EmaNeg/Power_Management_Unit_Tesi/Docs/Images/BAT_sym.png

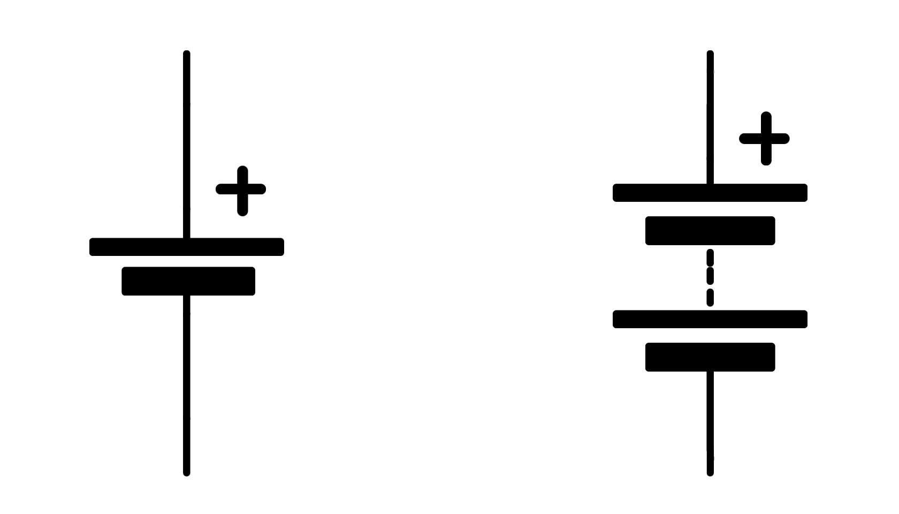
Docs/Images/BAT_sym.png
