EmaNeg/Power_Management_Unit_Tesi/Docs/Images/boost_schema.png

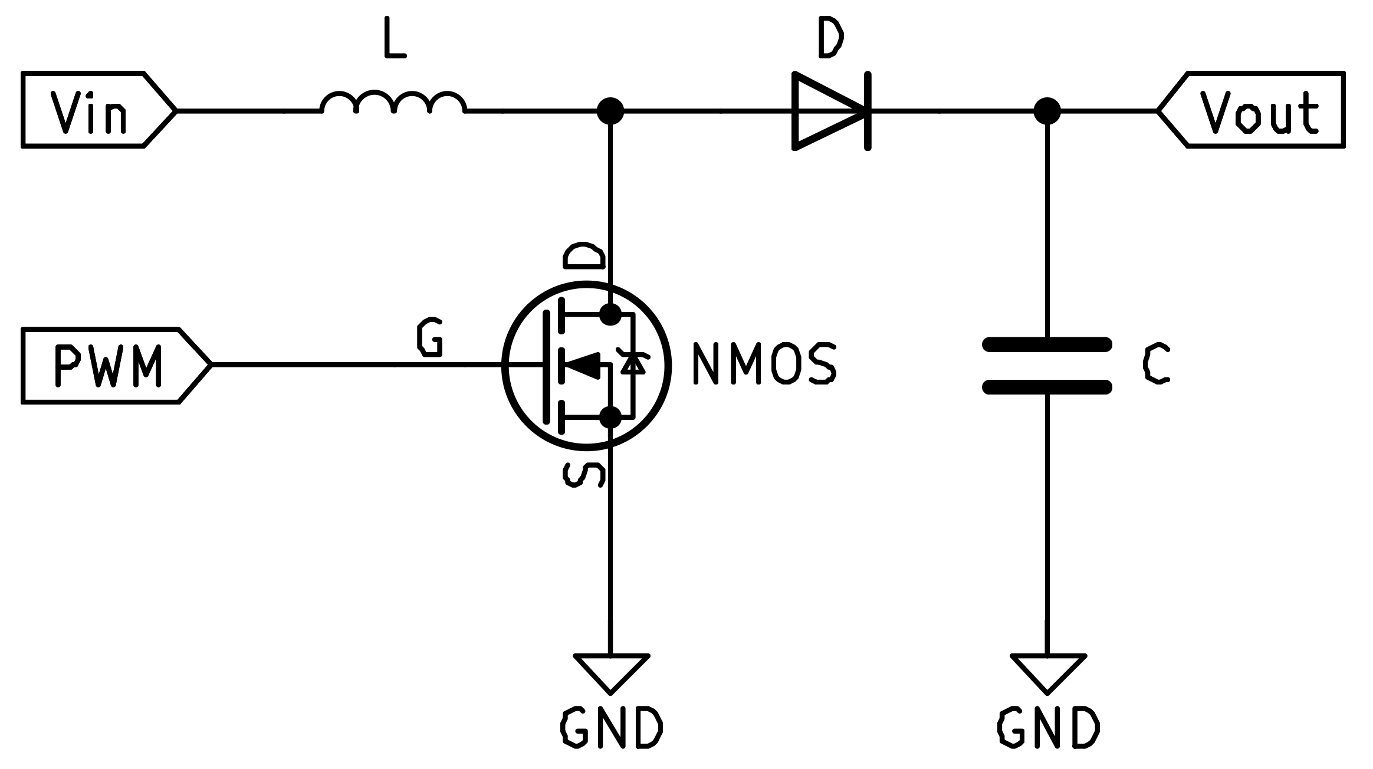
Docs/Images/boost_schema.png
