EmaNeg/Power_Management_Unit_Tesi/Docs/Images/bottom_real.png

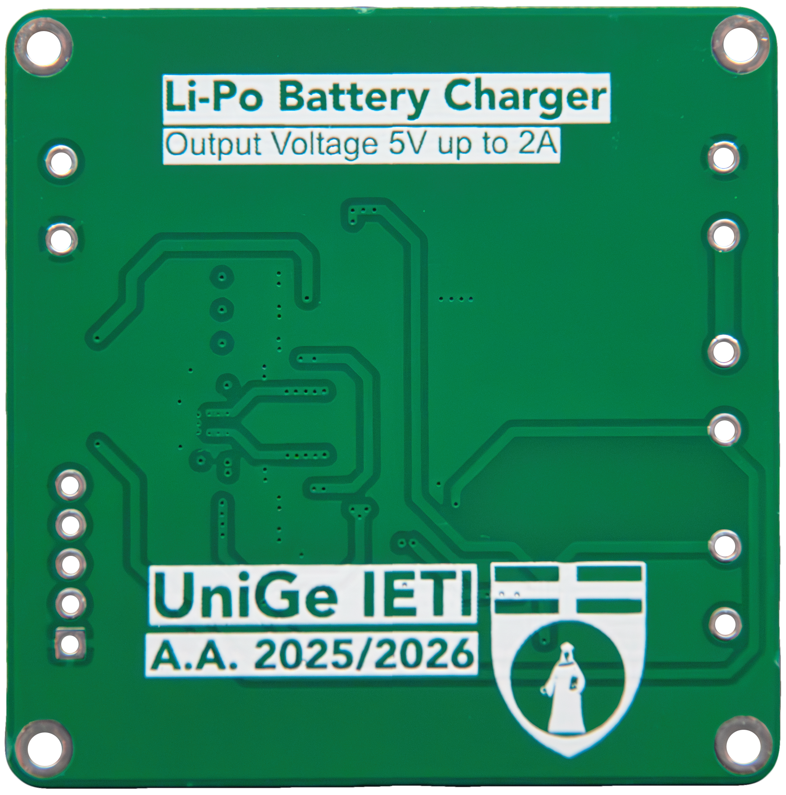
Docs/Images/bottom_real.png
