EmaNeg/Power_Management_Unit_Tesi/Docs/Images/buck-boost_schema.png

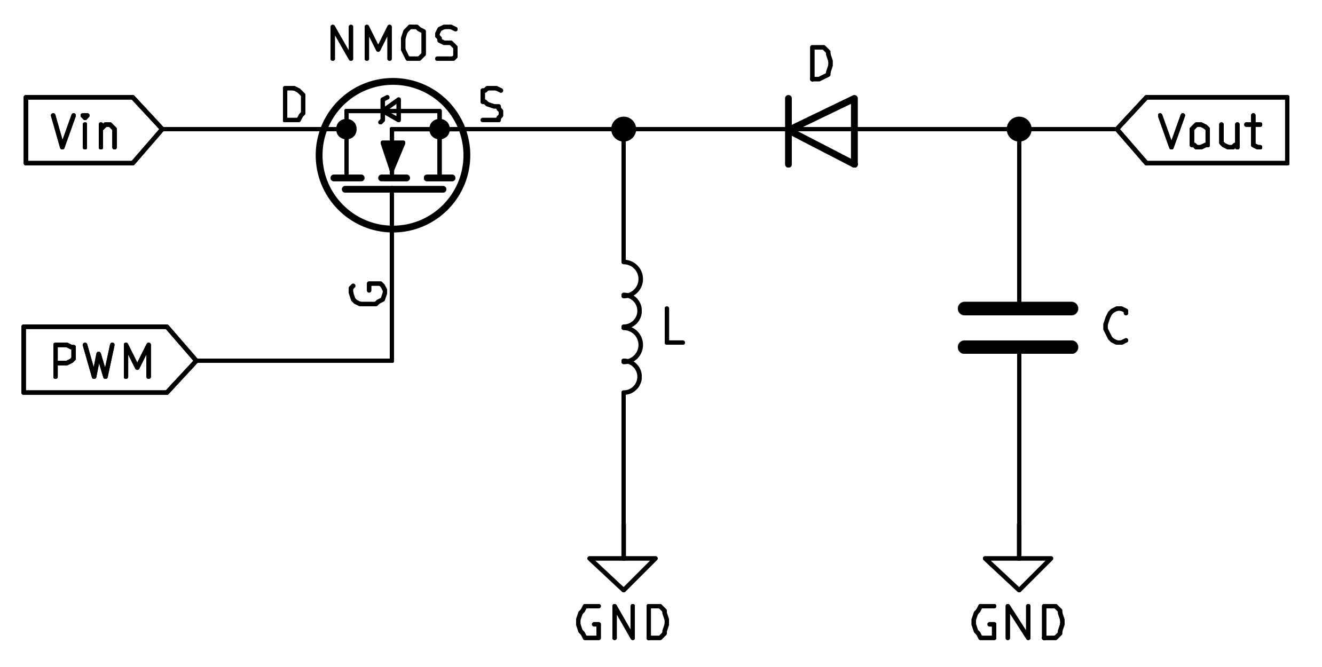
Docs/Images/buck-boost_schema.png
