EmaNeg/Power_Management_Unit_Tesi/Docs/Images/charge_pulse.png

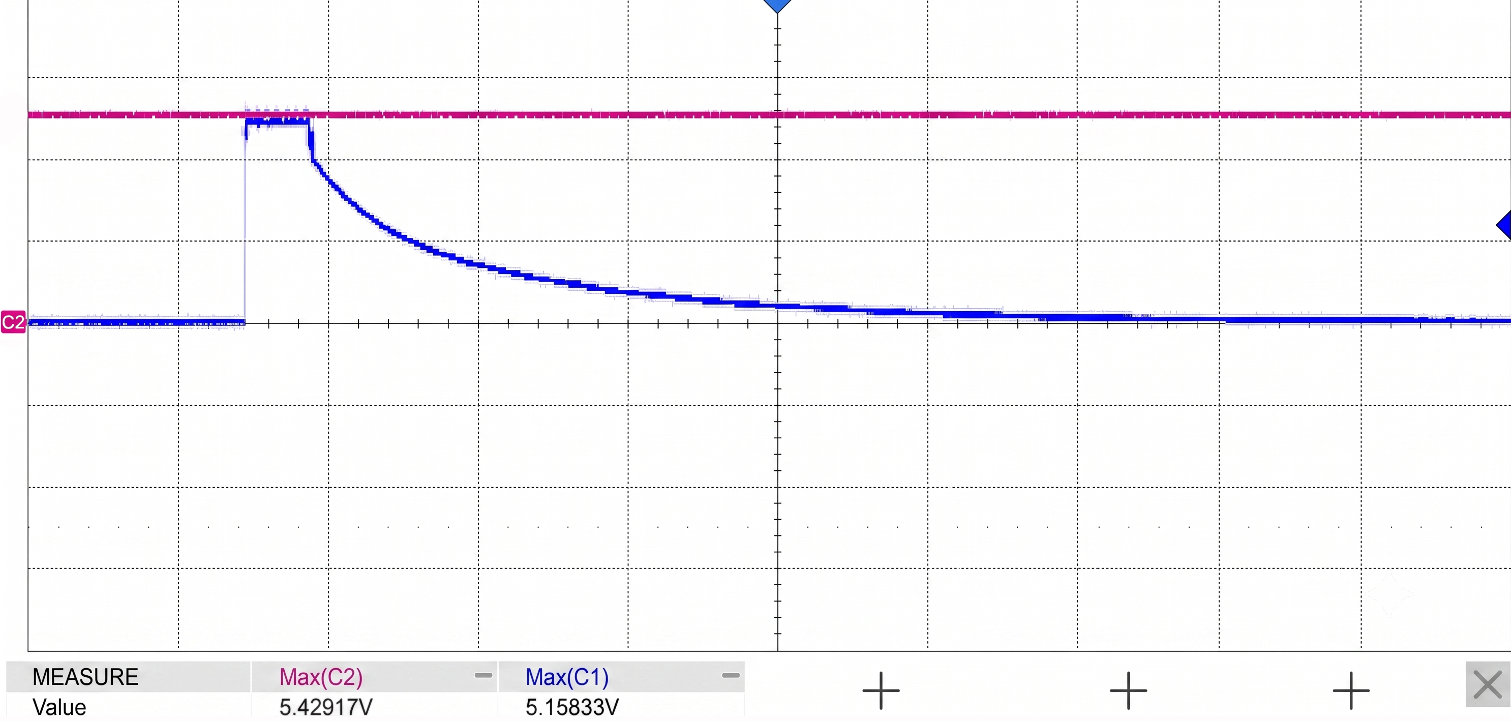
Docs/Images/charge_pulse.png
