EmaNeg/Power_Management_Unit_Tesi/Docs/Images/charge_pulse_black.png

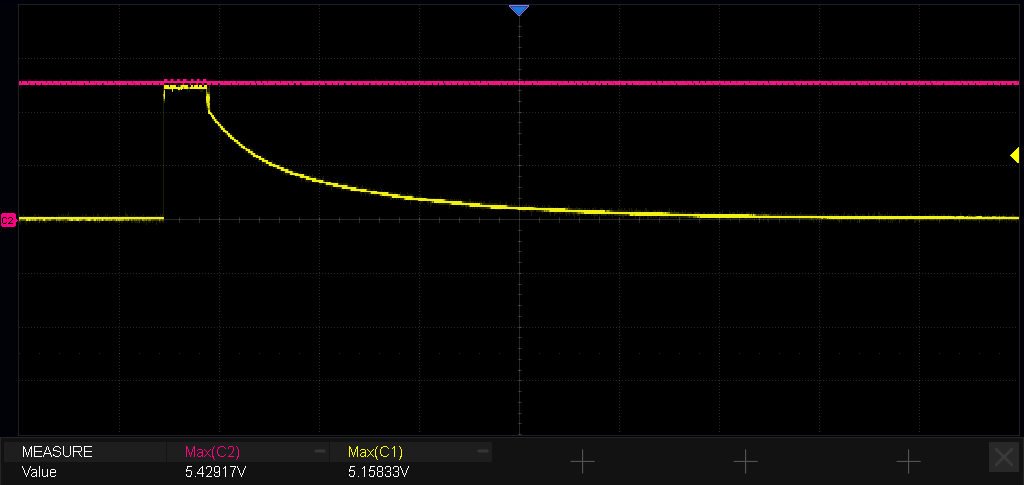
Docs/Images/charge_pulse_black.png
