EmaNeg/Power_Management_Unit_Tesi/Docs/Images/charge_pulse_zoom.png

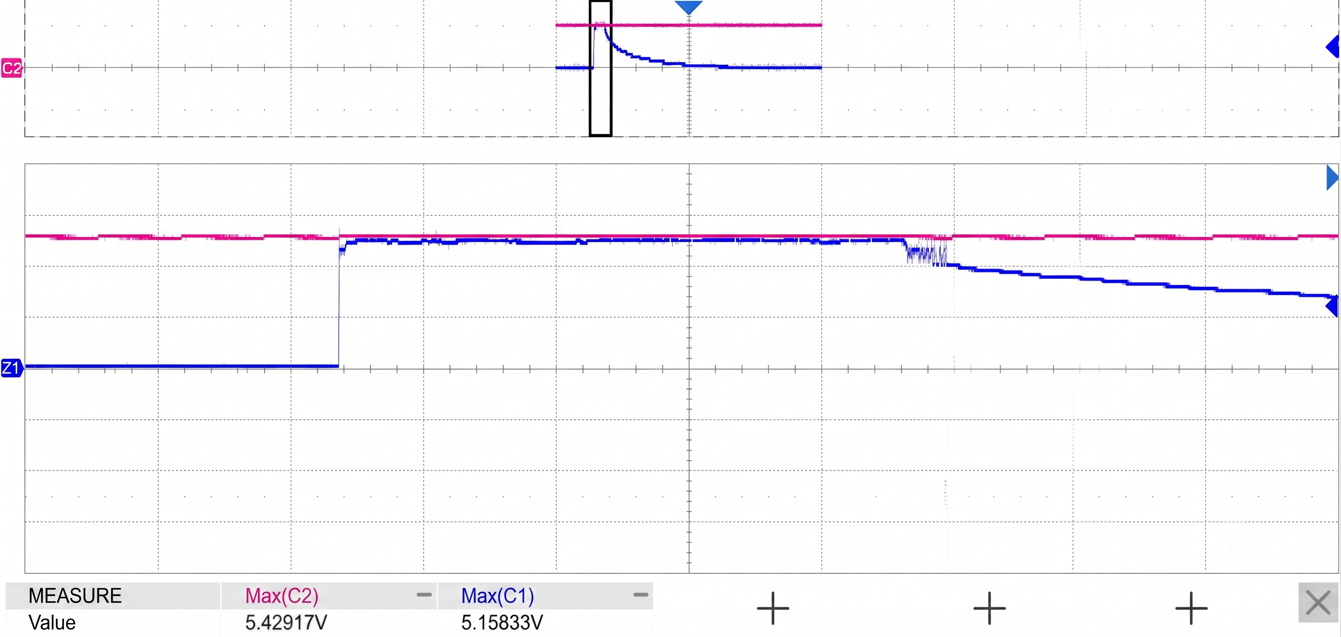
Docs/Images/charge_pulse_zoom.png
