EmaNeg/Power_Management_Unit_Tesi/Docs/Images/charging_header_switch.png

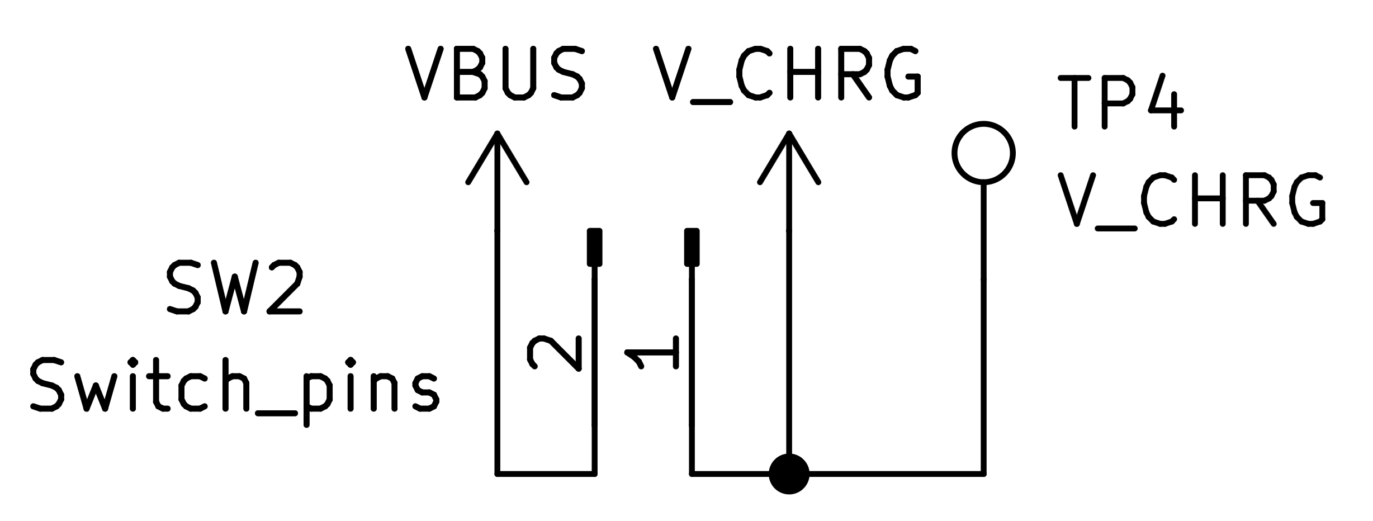
Docs/Images/charging_header_switch.png
