EmaNeg/Power_Management_Unit_Tesi/Docs/Images/charging_ic.png

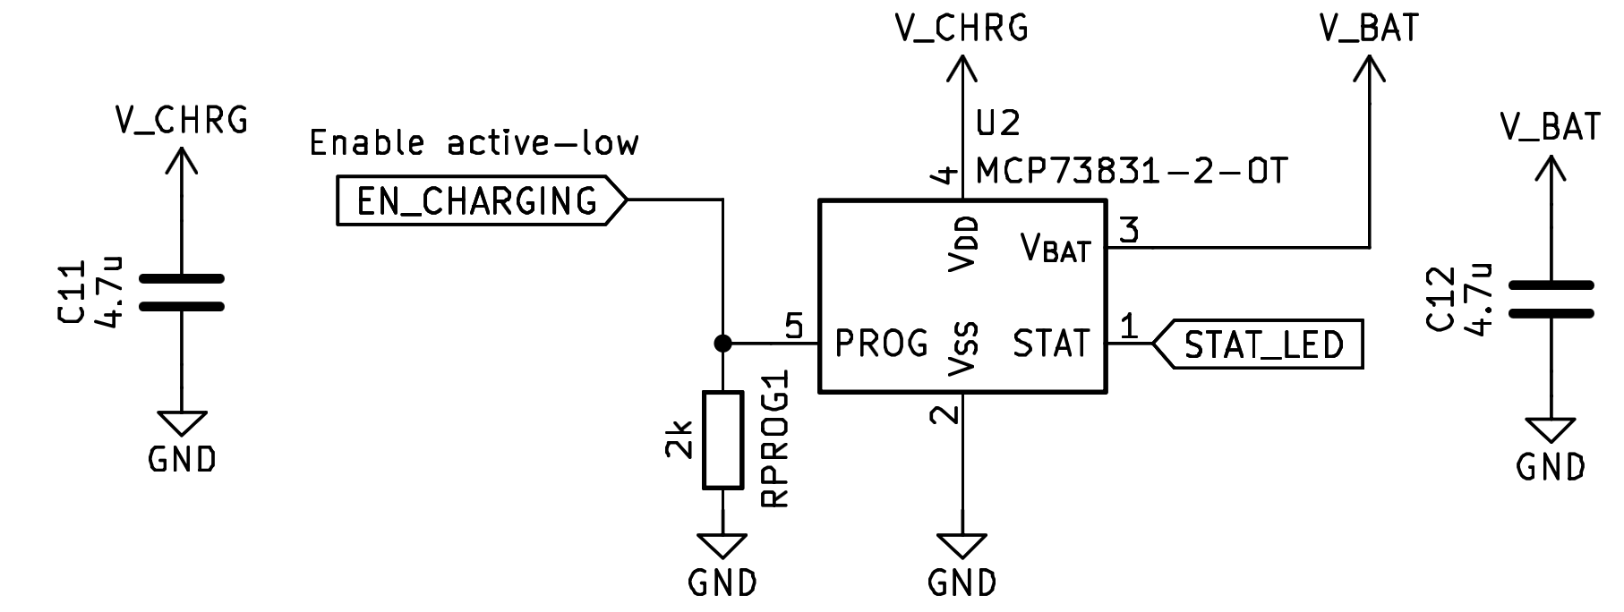
Docs/Images/charging_ic.png
