EmaNeg/Power_Management_Unit_Tesi/Docs/Images/dc-dc_bat.png

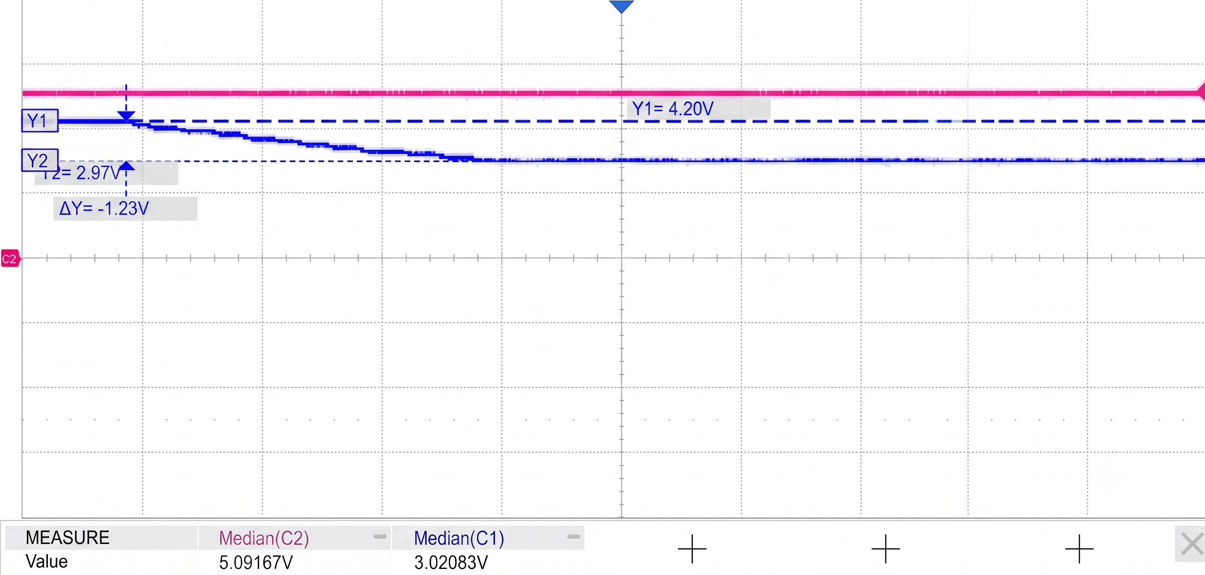
Docs/Images/dc-dc_bat.png
