EmaNeg/Power_Management_Unit_Tesi/Docs/Images/dc-dc_bat_black.png

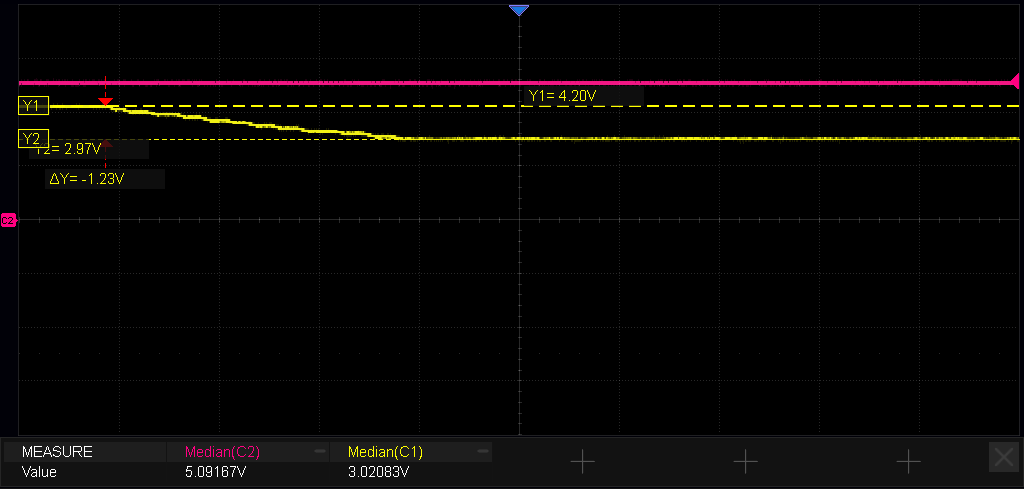
Docs/Images/dc-dc_bat_black.png
