EmaNeg/Power_Management_Unit_Tesi/Docs/Images/dc-dc_ext.jpg

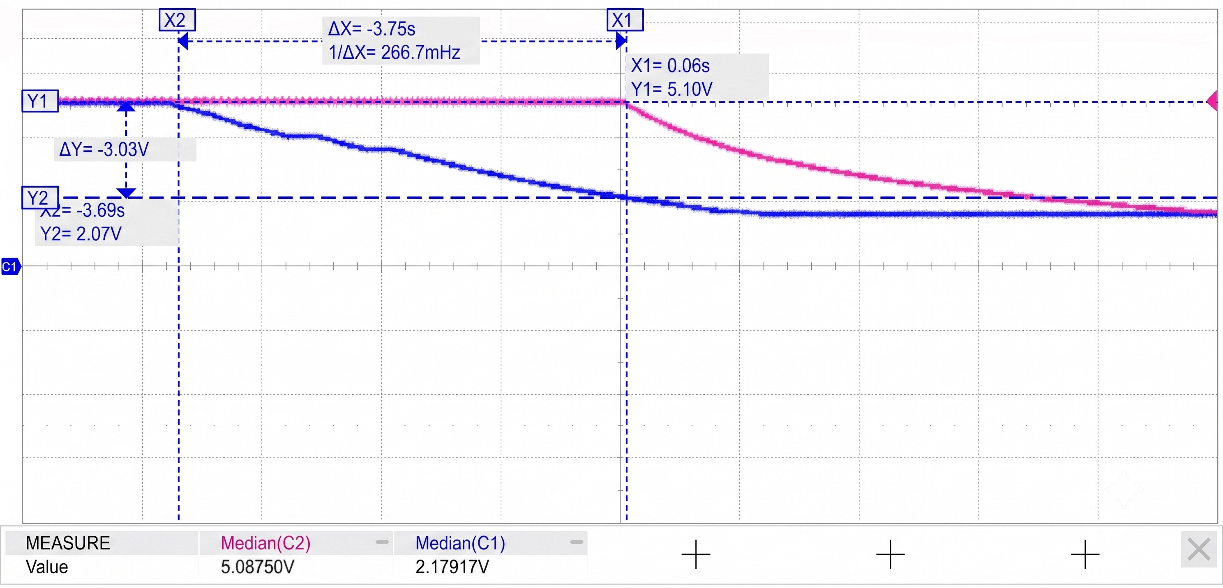
Docs/Images/dc-dc_ext.jpg
