EmaNeg/Power_Management_Unit_Tesi/Docs/Images/dc-dc_ext_black.png

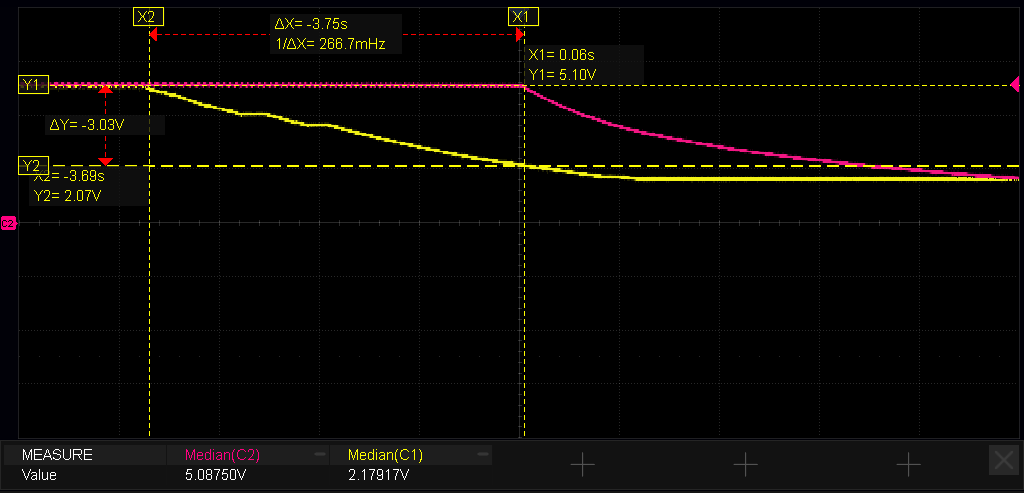
Docs/Images/dc-dc_ext_black.png
