EmaNeg/Power_Management_Unit_Tesi/Docs/Images/DC_DC.png

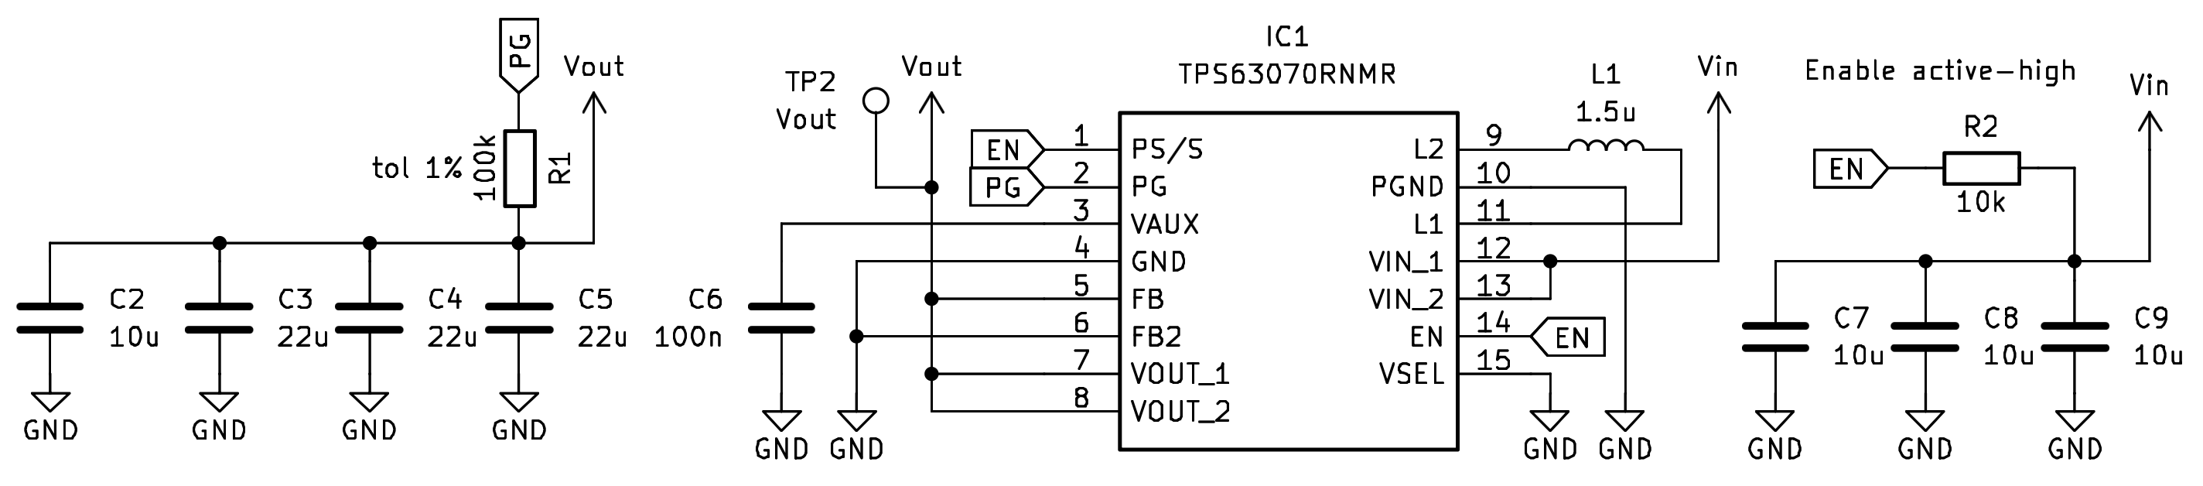
Docs/Images/DC_DC.png
