EmaNeg/Power_Management_Unit_Tesi/Docs/Images/dip_switch.png

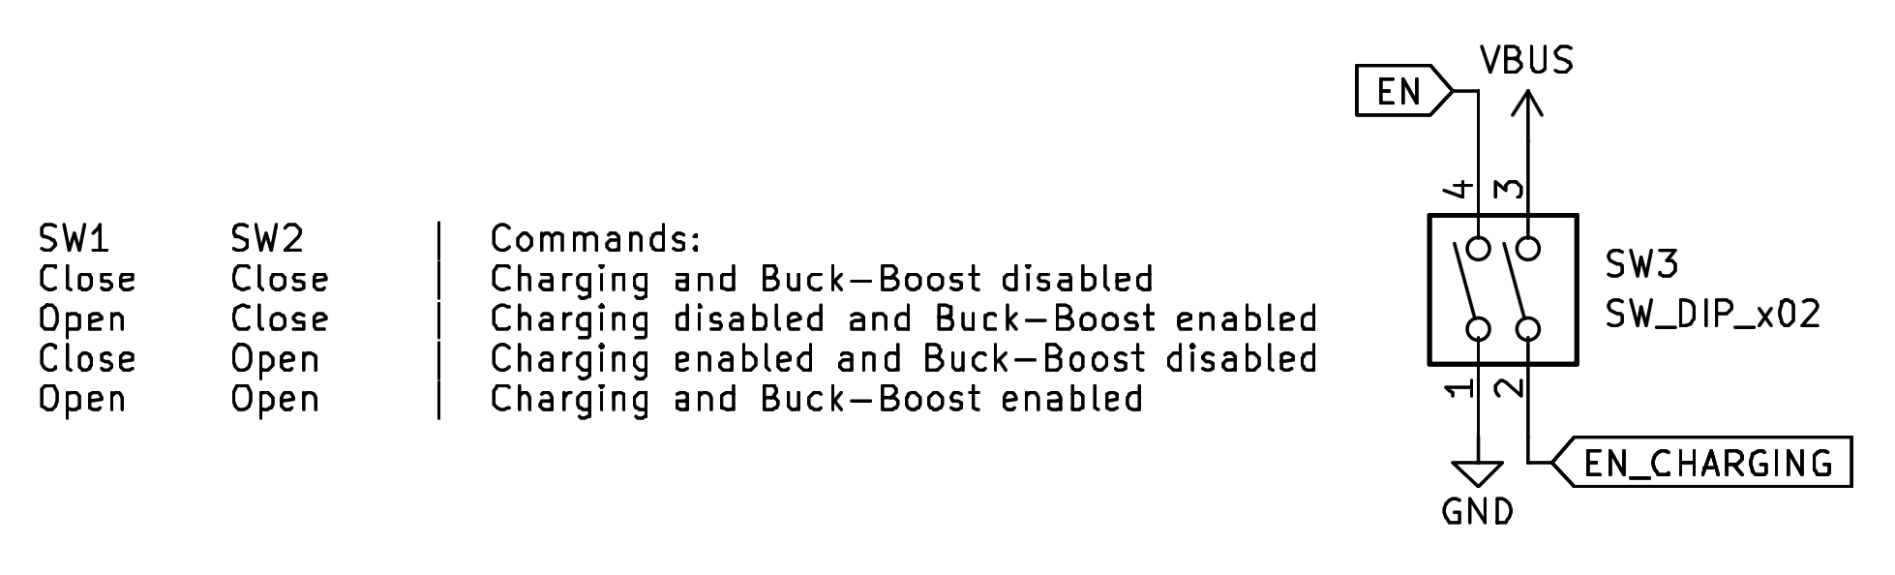
Docs/Images/dip_switch.png
