EmaNeg/Power_Management_Unit_Tesi/Docs/Images/en_charge.png

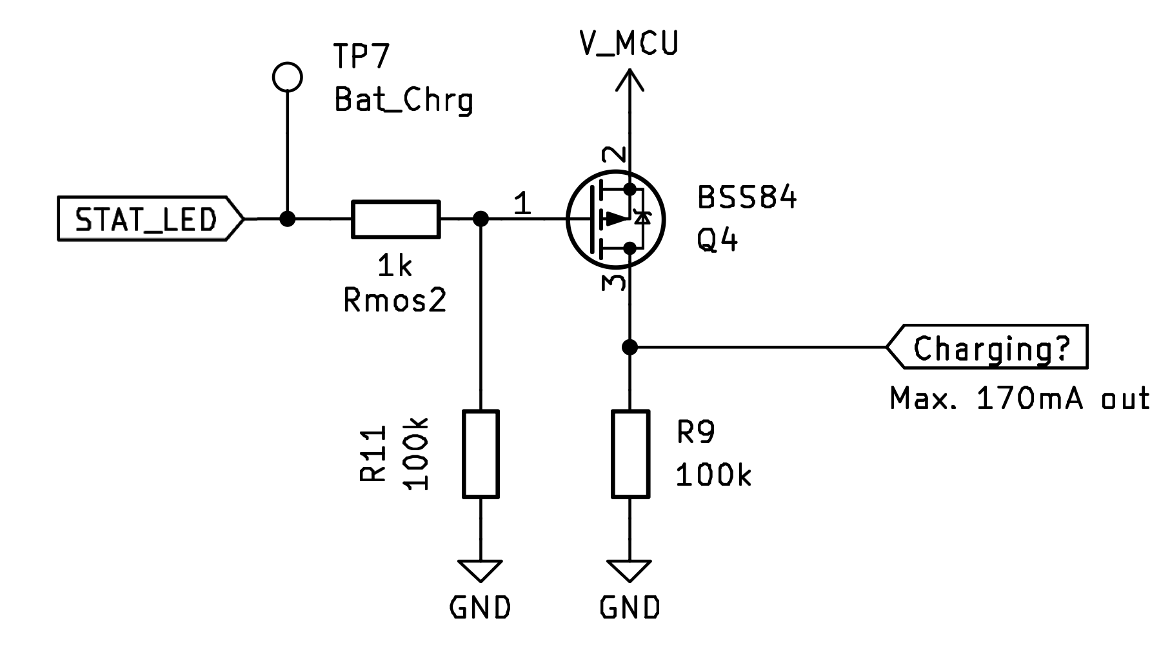
Docs/Images/en_charge.png
