EmaNeg/Power_Management_Unit_Tesi/Docs/Images/ENV_layout.png

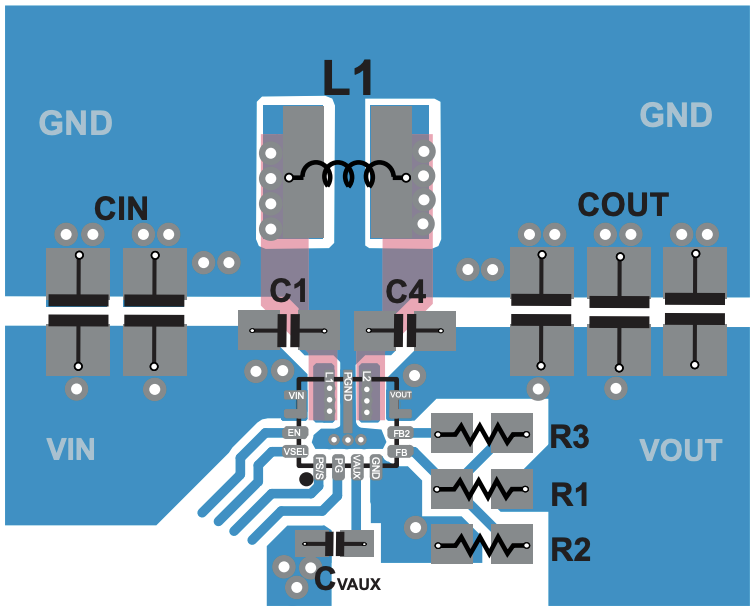
Docs/Images/ENV_layout.png
