EmaNeg/Power_Management_Unit_Tesi/Docs/Images/Fixed_LDO.png

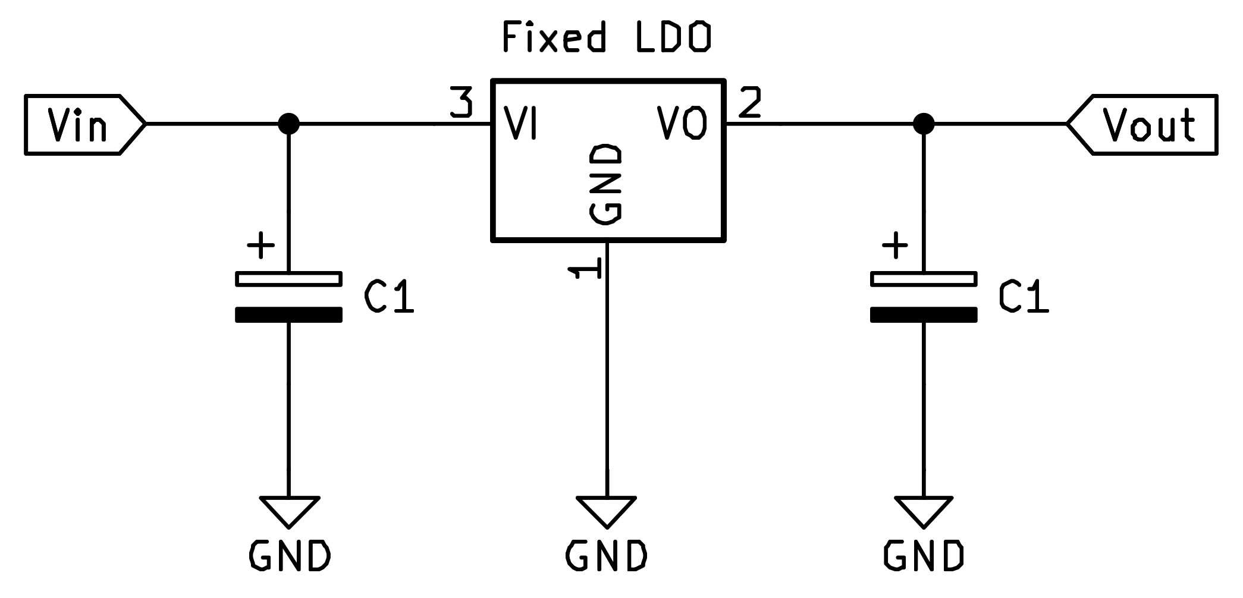
Docs/Images/Fixed_LDO.png
