EmaNeg/Power_Management_Unit_Tesi/Docs/Images/led_charge.png

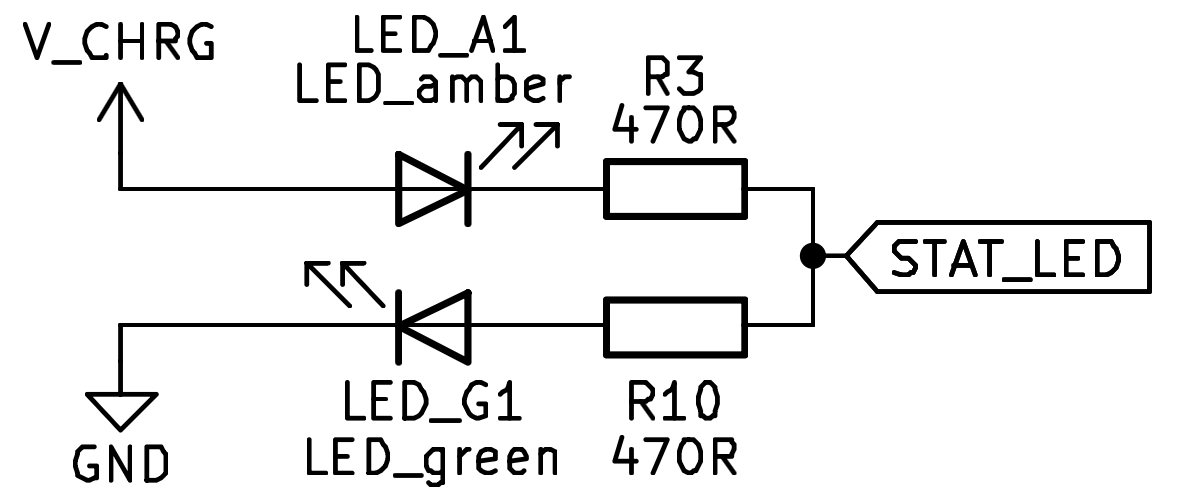
Docs/Images/led_charge.png
