EmaNeg/Power_Management_Unit_Tesi/Docs/Images/protection.png

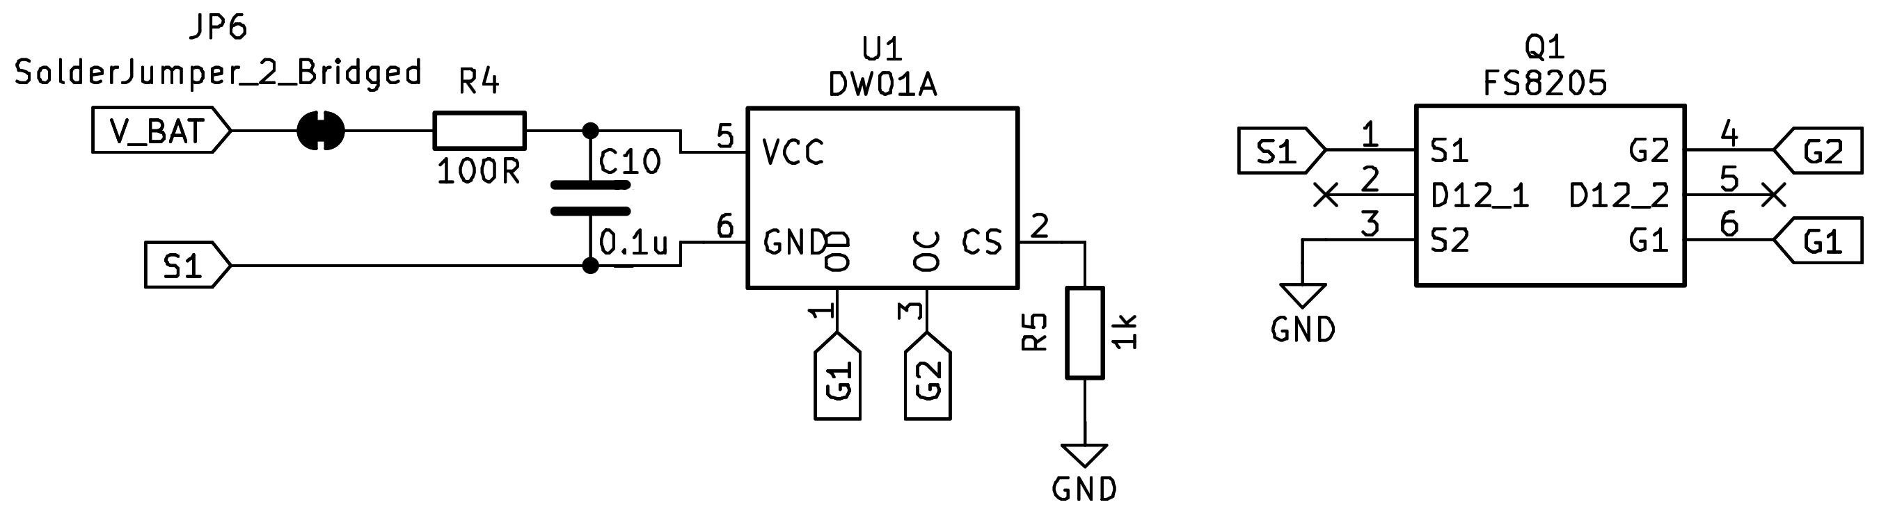
Docs/Images/protection.png
