EmaNeg/Power_Management_Unit_Tesi/Docs/Images/real.png

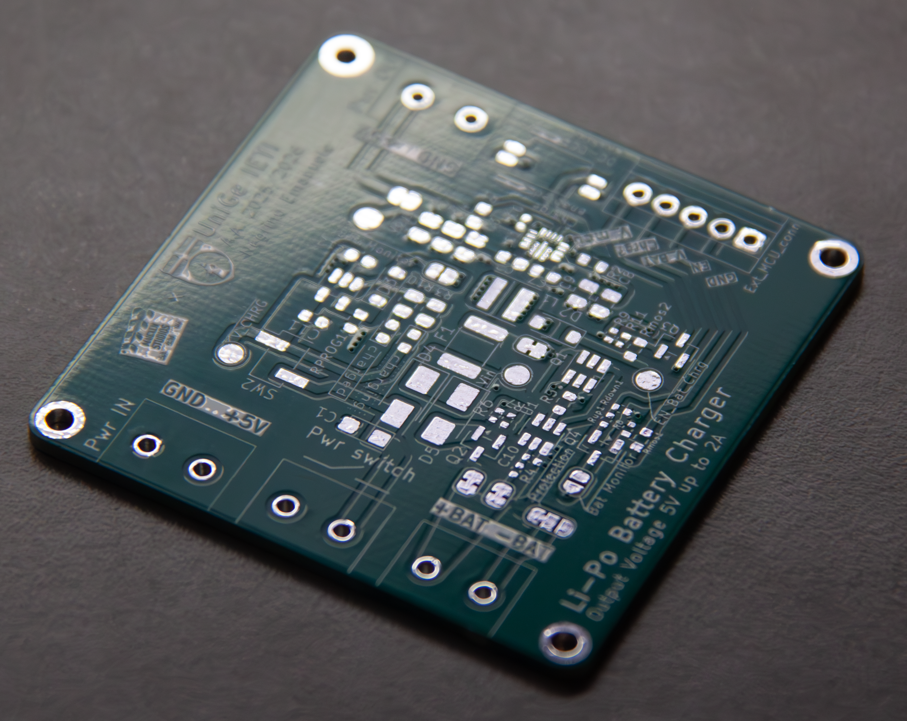
Docs/Images/real.png
