EmaNeg/Power_Management_Unit_Tesi/Docs/Images/render_comp.png

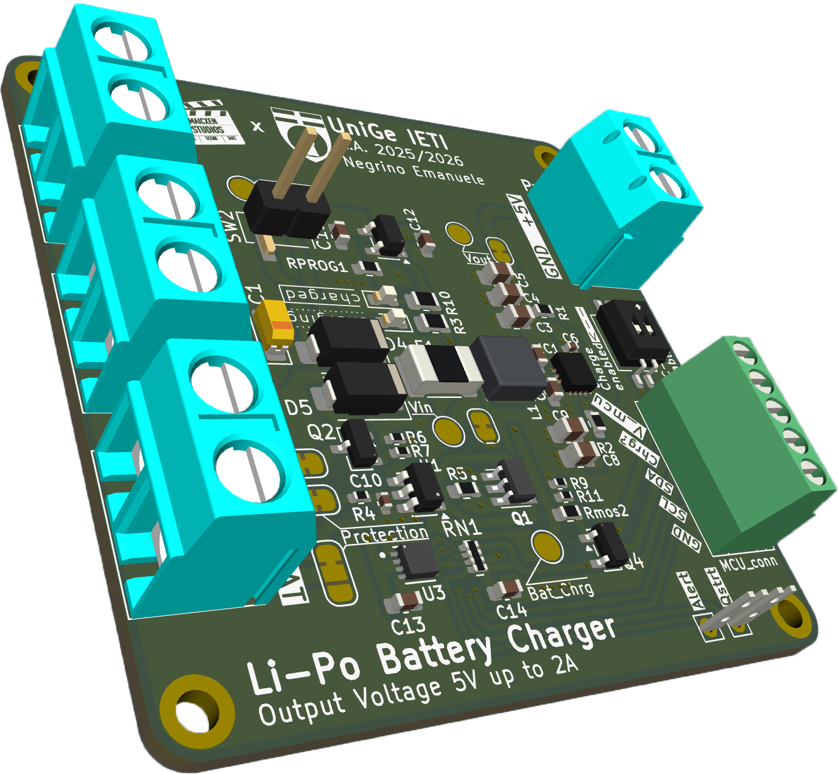
Docs/Images/render_comp.png
