EmaNeg/Power_Management_Unit_Tesi/Docs/Images/ripple_uscita.png

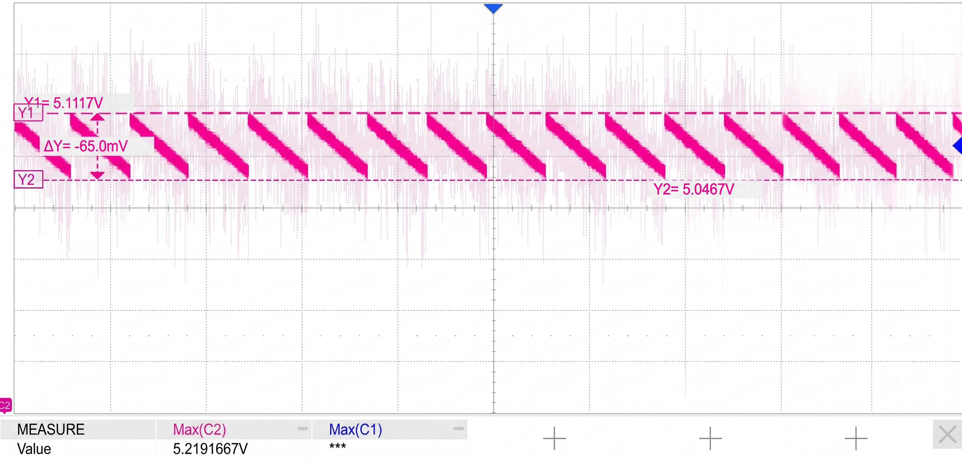
Docs/Images/ripple_uscita.png
