EmaNeg/Power_Management_Unit_Tesi/Docs/Images/ripple_uscita_freq.png

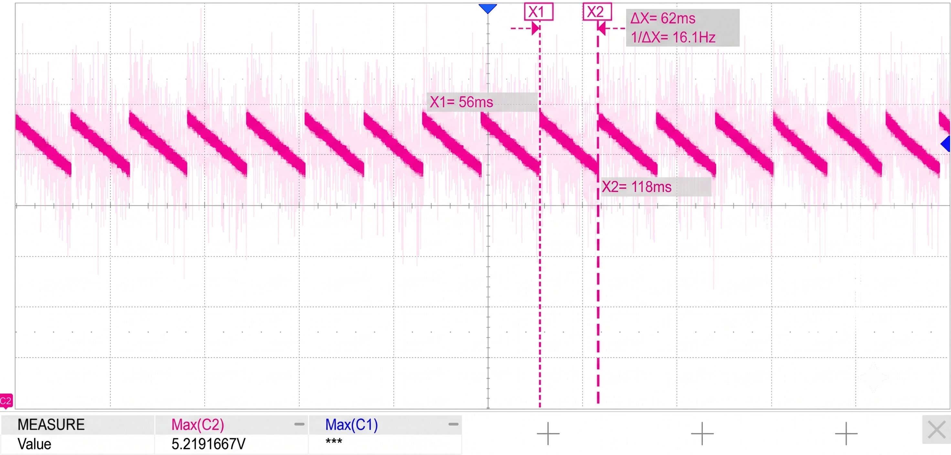
Docs/Images/ripple_uscita_freq.png
