EmaNeg/Power_Management_Unit_Tesi/Docs/Images/risp_gradino_bat.png

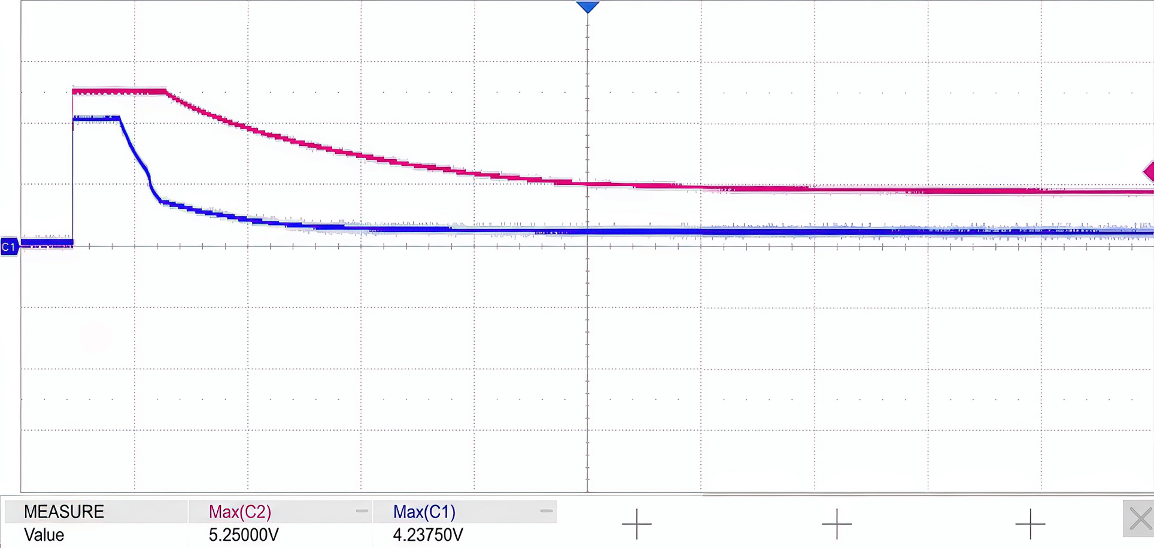
Docs/Images/risp_gradino_bat.png
