EmaNeg/Power_Management_Unit_Tesi/Docs/Images/risp_gradino_ext_black.png

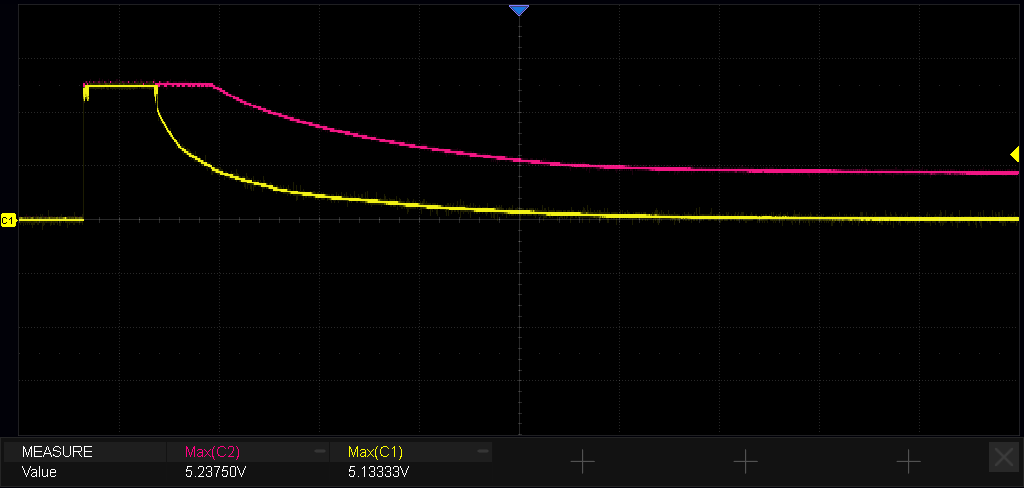
Docs/Images/risp_gradino_ext_black.png
