EmaNeg/Power_Management_Unit_Tesi/Docs/Images/sim_en_charge.png

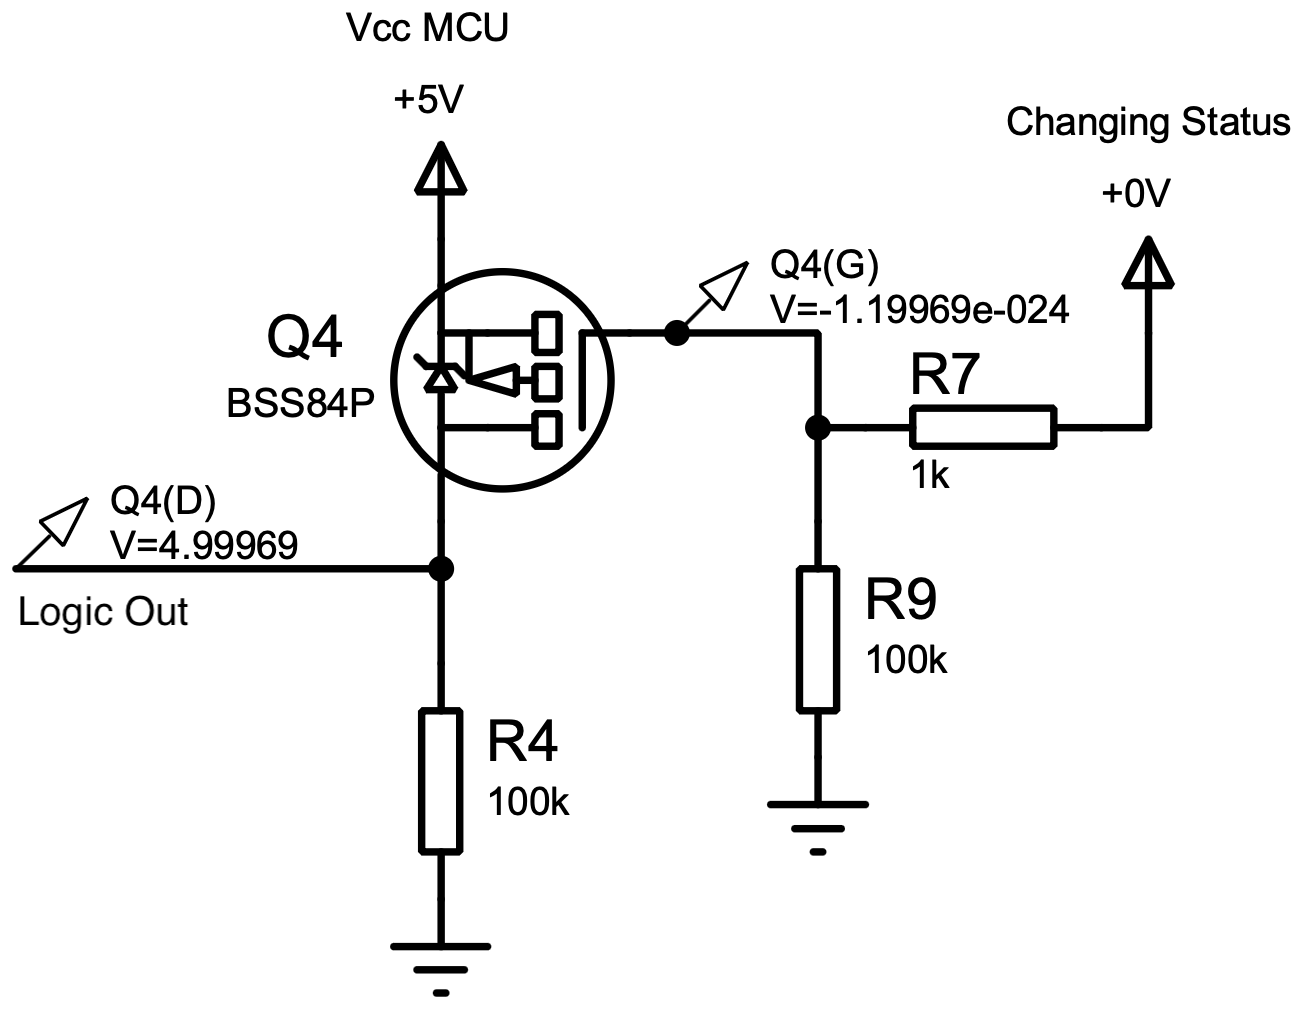
Docs/Images/sim_en_charge.png
