EmaNeg/Power_Management_Unit_Tesi/Docs/Images/sim_power_switch.png

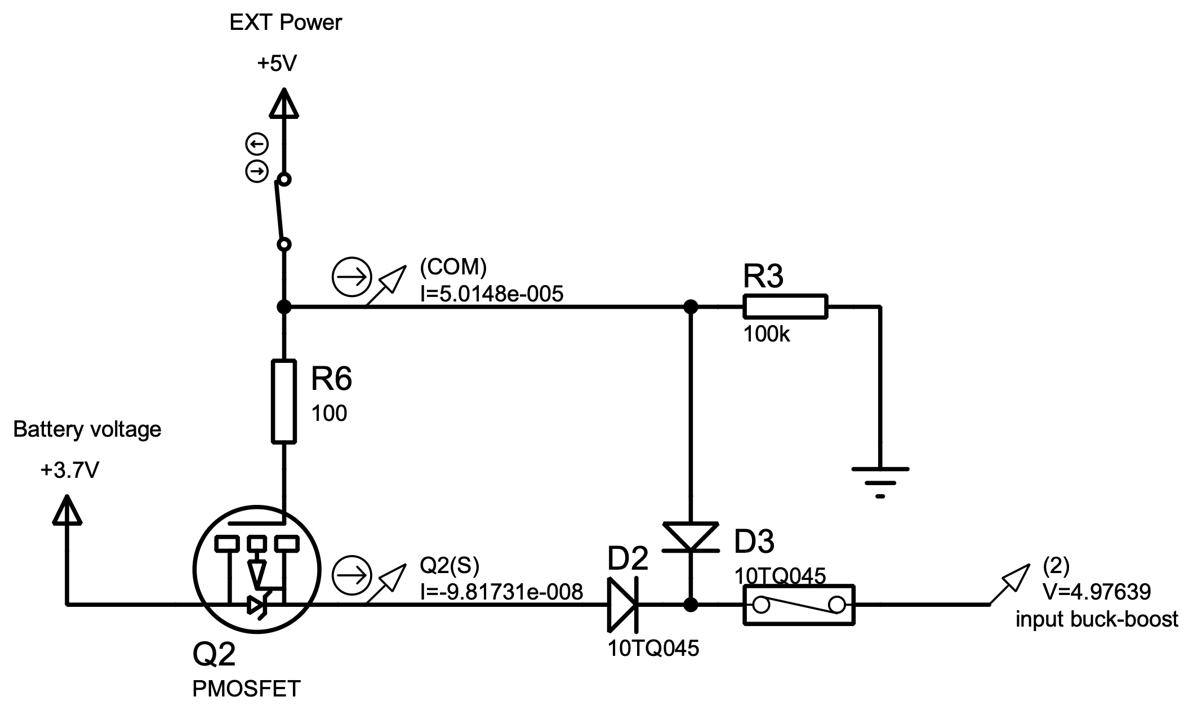
Docs/Images/sim_power_switch.png
