EmaNeg/Power_Management_Unit_Tesi/Docs/Images/sim_power_switch_2.png

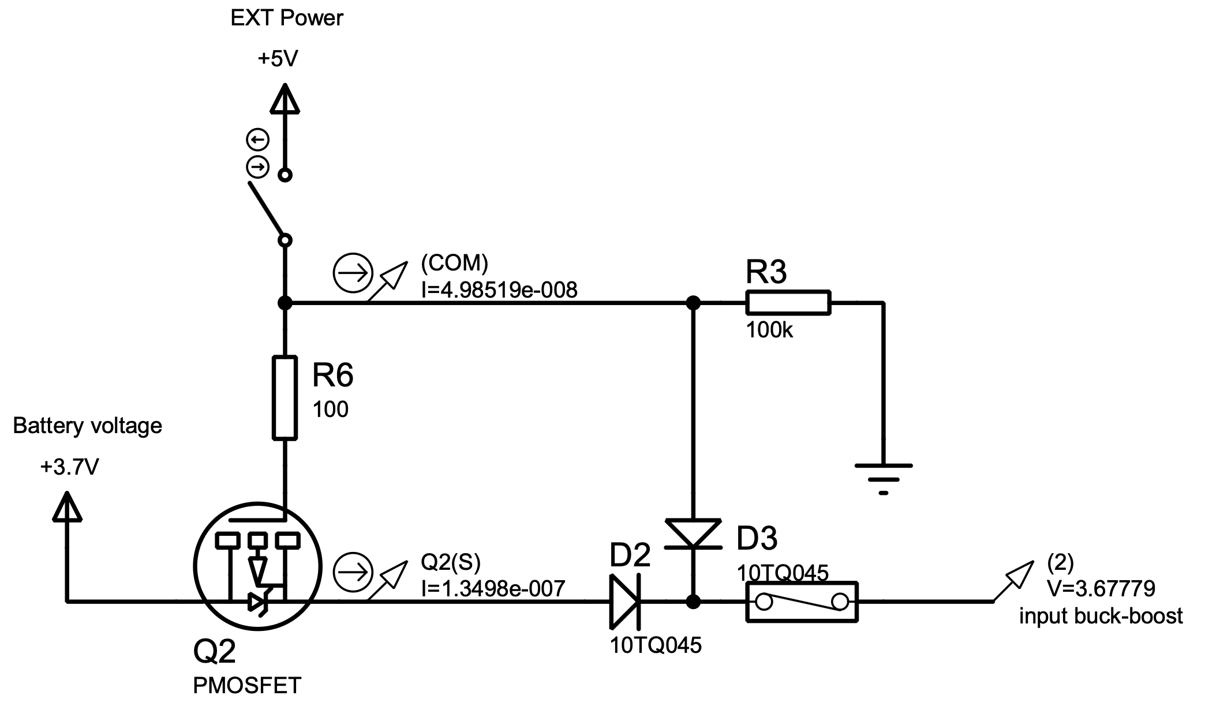
Docs/Images/sim_power_switch_2.png
