EmaNeg/Power_Management_Unit_Tesi/Docs/Images/source_switcher.png

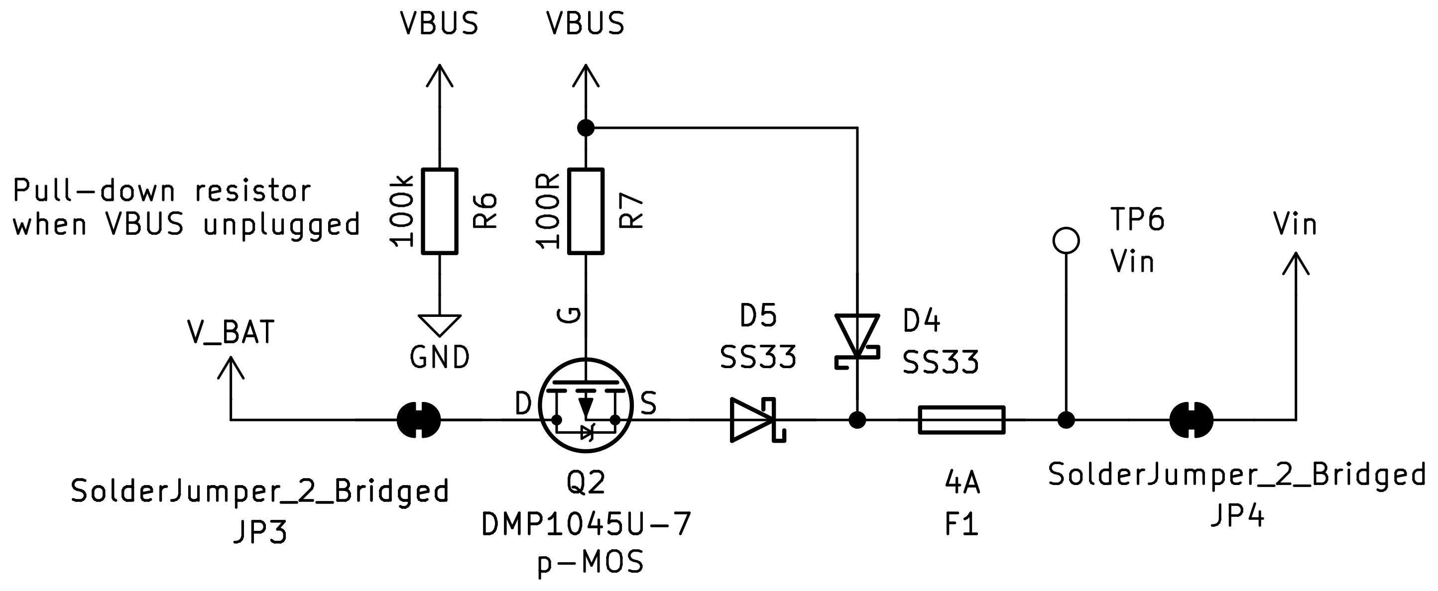
Docs/Images/source_switcher.png
