EmaNeg/Power_Management_Unit_Tesi/Docs/Images/temperatura_graf.png

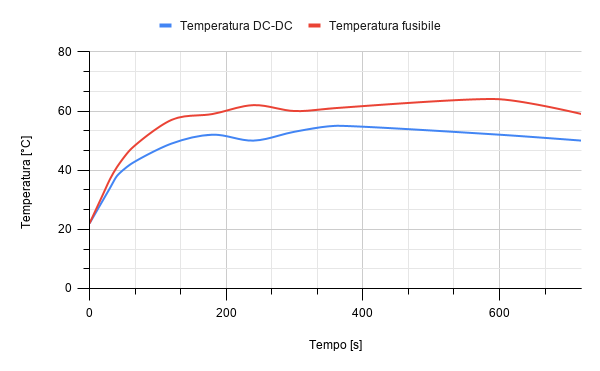
Docs/Images/temperatura_graf.png
