EmaNeg/Power_Management_Unit_Tesi/Docs/Images/top_real.png

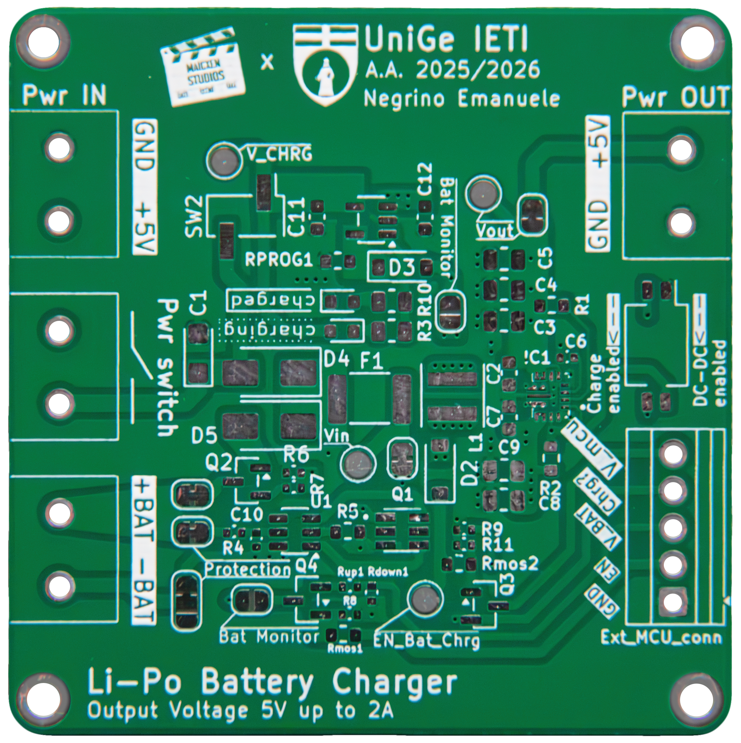
Docs/Images/top_real.png
