EmaNeg/Power_Management_Unit_Tesi/Docs/Images/top_render_comp.png

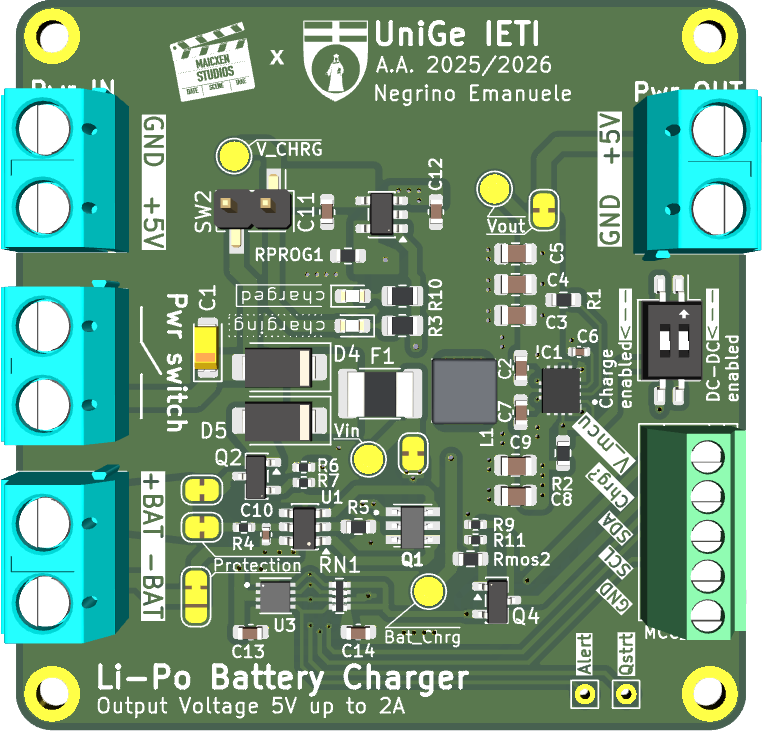
Docs/Images/top_render_comp.png
