EmaNeg/Power_Management_Unit_Tesi/Docs/Images/top_render_half.png

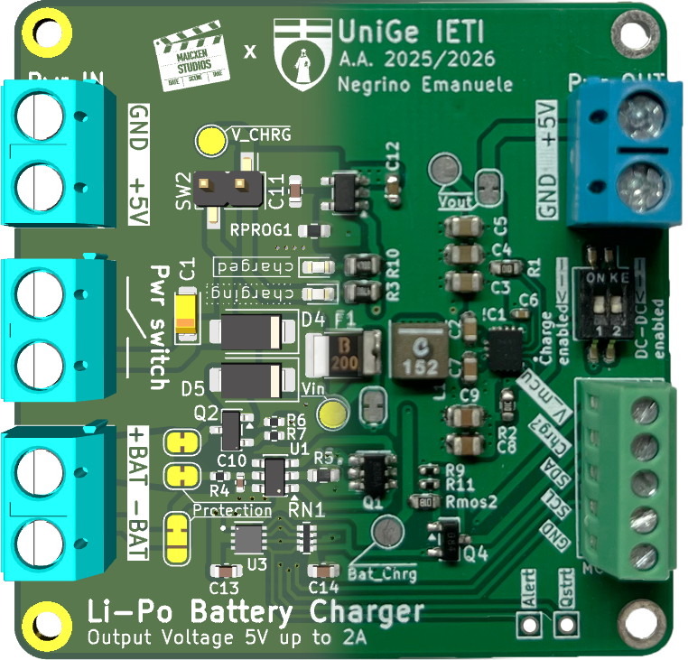
Docs/Images/top_render_half.png
