EmaNeg/Power_Management_Unit_Tesi/Docs/Images/assembled_real2.png

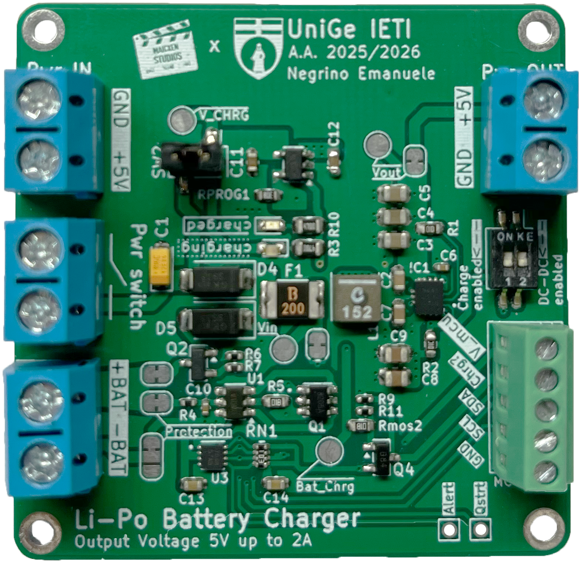
Docs/Images/assembled_real2.png
