EmaNeg/Power_Management_Unit_Tesi/Docs/Images/assembled_real.png

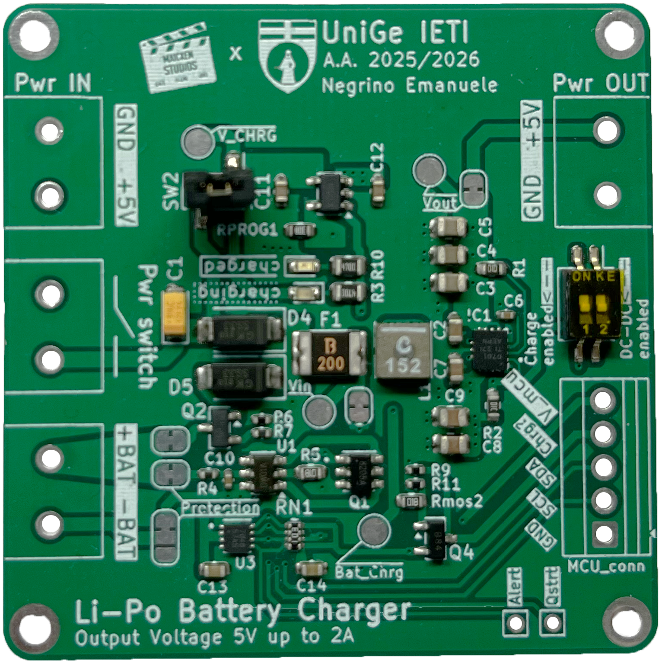
Docs/Images/assembled_real.png
